maxgohren/ESPip-Boy/ESPip-Boy_OS/loading_screen.h

/* Generated from https://notisrac.github.io/FileToCArray/ */
#define IMG_HEIGHT 100
#define IMG_WIDTH 100

#if 0
  gfx->fillScreen(BACKGROUND);
  gfx->draw16bitRGBBitmap(gfx->width() / 2 - IMG_WIDTH / 2 , 
                          gfx->height() / 2 - IMG_HEIGHT /2, 
                          (const uint16_t*)vault_boy_pip_boy_color, 
                          IMG_HEIGHT, 
                          IMG_WIDTH);
  DEBUG_PRINTF("Finished drawing loading screen: w: %d, h: %d\n\n", gfx->width(), gfx->height());

  gfx->setTextColor(RGB565_WHITE, RGB565_BLACK);
  int textSize = gfx->width() / 94;
  gfx->setTextSize(textSize, textSize, 2 /* pixel_margin */);
  gfx->setCursor(20, 50); // Centered above pip
#endif

// array size is 20000
const uint16_t vault_boy_pip_boy_color[] PROGMEM  = {
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
};
#include "log.h"
