maxgohren/ESPip-Boy/ESPip-Boy_OS/termiwatch.cpp

/* Inspired by u/quarl0w and
 * https://github.com/kuglee/TermiWatch?tab=readme-ov-file 
 */

#include "log.h"
#include <Arduino_GFX_Library.h>
#include "termiwatch.h"
#include "flash.h"
#include "fuel.h"
#include "imu.h"
#include "weather.h"
#include "rtc.h"
#include "pinout.h"
#include "freertos/FreeRTOS.h"
#include "freertos/task.h"

#define BACKGROUND RGB565_BLACK
#define LCD_WIDTH  240
#define LCD_HEIGHT 280

int  textSize;
char textLine[100];
char subStr[50];

// ----- FreeRTOS -----
SemaphoreHandle_t spiMutex;
TaskHandle_t displayUpdateTaskHandle = NULL;

// ----- Display Setup -----

Arduino_DataBus *bus = new Arduino_ESP32SPI(LCD_DC, LCD_CS, LCD_SCK, LCD_MOSI);

Arduino_GFX *gfx = new Arduino_ST7789(
  bus,
  LCD_RST,          // RST pin
  0,                // rotation (0–3)
  true,             // IPS
  LCD_WIDTH,
  LCD_HEIGHT,
  0, 20, 0, 0       // x, y offsets for 240x280 ST7789 panels
);

static void draw_termiwatch()
{
  // TODO if nothing changes, do not draw
  // keep track of display changes, only draw things that change
  // keep track of item state versus display state
  // if item state changes, make call to change corresponding display state
    int vpos = 35;
    int hpos = 15;
    int gap = 25;

    // Digital clock logic
    // TODO abstract into clock.h
    time_t now;
    time(&now);
    struct tm *tmLocal = localtime(&now); // must have called rtc.init() to set TZ

    /* user@watch:~ $now */
    snprintf(textLine, sizeof(textLine), "max@watch:~ $ now");
    gfx->setTextColor(RGB565_WHITE, RGB565_BLACK);
    gfx->setCursor(hpos, vpos);
    gfx->print(textLine);
    vpos += gap;

    /* Time */
    strftime(subStr, sizeof(subStr), "%I:%M:%S %p", tmLocal);
    snprintf(textLine, sizeof(textLine), "[TIME] %s", subStr);
    gfx->setTextColor(RGB565_CYAN, RGB565_BLACK);
    gfx->setCursor(hpos, vpos);
    gfx->print(textLine);
    vpos += gap;

    /* Date */
    strftime(subStr, sizeof(subStr), "%a %e %b", tmLocal);
    snprintf(textLine, sizeof(textLine), "[DATE] %s", subStr);
    gfx->setTextColor(RGB565_RED, RGB565_BLACK);
    gfx->setCursor(hpos, vpos);
    gfx->print(textLine);
    vpos += gap;

    /* TEMP */
    WeatherData currentWeather = WeatherService_getWeather();
    // TODO only update when weather data changes, not every second
    snprintf(textLine, sizeof(textLine), "[TEMP] %.1f C", currentWeather.temperature);
    gfx->setTextColor(RGB565_YELLOW, RGB565_BLACK);
    gfx->setCursor(hpos, vpos);
    gfx->print(textLine);
    vpos += gap;

    /* BATV */
    // rough clear logic
    // static old_v = 0;
    /* int v = fuelGauge.readVoltage();
     * if (v != old_v)
     *  gfx->drawRect() (or even just an empty line)
     */
    snprintf(textLine, sizeof(textLine), "[BATV] %d mV", fuelGauge.readVoltage());
    gfx->setCursor(hpos, vpos);
    gfx->setTextColor(RGB565_ORANGE, RGB565_BLACK);
    gfx->print(textLine);
    vpos += gap;

    /* BATA */
    snprintf(textLine, sizeof(textLine), "[BATA] %d mA", fuelGauge.readCurrent());
    gfx->setTextColor(RGB565_SLATEGRAY, RGB565_BLACK);
    gfx->setCursor(hpos, vpos);
    gfx->print(textLine);
    vpos += gap;

    /* STEP */
    snprintf(textLine, sizeof(textLine), "[STEP] %d", getStepCount());
    gfx->setTextColor(RGB565_CHARTREUSE, RGB565_BLACK);
    gfx->setCursor(hpos, vpos);
    gfx->print(textLine);
    vpos += gap;

    /* FLSH */
    snprintf(textLine, sizeof(textLine), "[FLSH] %s", flash_on() ? "ON" : "OFF");
    gfx->setTextColor(RGB565_TURQUOISE, RGB565_BLACK);
    gfx->setCursor(hpos, vpos);
    gfx->print(textLine);
    vpos += gap;

    snprintf(textLine, sizeof(textLine), "max@watch:~ $");
    gfx->setTextColor(RGB565_WHITE, RGB565_BLACK);
    gfx->setCursor(hpos, vpos);
    gfx->print(textLine);
    vpos += gap;
}

static void DisplayUpdateTask(void *parameter)
{
  TickType_t lastWakeTime = xTaskGetTickCount();

  // IMMEDIATELY DRAW WHEN CALLED ON STARTUP
  if (xSemaphoreTake(spiMutex, portMAX_DELAY))
  {
    draw_termiwatch();
    xSemaphoreGive(spiMutex);
  }

  while(true)
  {
    // Wait exactly 1 second
    vTaskDelayUntil(&lastWakeTime, pdMS_TO_TICKS(1000));

    // Protect SPI bus from any other transactions
    if (xSemaphoreTake(spiMutex, portMAX_DELAY))
    {
      draw_termiwatch();
      xSemaphoreGive(spiMutex);
    }
  }

}

void init_termiwatch()
{
    DEBUG_PRINTF("Init display w: %d, h: %d\n", LCD_WIDTH, LCD_HEIGHT);

    spiMutex = xSemaphoreCreateMutex();

    if (xSemaphoreTake(spiMutex, portMAX_DELAY))
    {
      if (!gfx->begin())
      {
        DEBUG_PRINTLN("gfx->begin() failed!");
      }

      //gfx->fillScreen(BACKGROUND); // misses bottom edge of screen
      gfx->fillRect(0, 0, LCD_WIDTH, 320, RGB565_BLACK);

      textSize = 2.5; // pixel multiplier
      gfx->setTextSize(textSize, textSize, 2 /* pixel_margin */);

      xSemaphoreGive(spiMutex);
    }

    // Start drawing task
    xTaskCreatePinnedToCore(
        DisplayUpdateTask,
        "DisplayUpdateTask",
        4096,
        NULL,
        2, // higher priority than display backlight fade
        &displayUpdateTaskHandle,
        1); // same core
}
